giacomomellone/cicala/hardware/rev_b/pcb/models/README.md

# Component envelopes

These original, simplified STEP models restore the missing component
bodies in KiCad. The inherited models are generated by `../../../tools/pcb/make_component_models.py`
with CadQuery and use CERN-OHL-S-2.0, like the project hardware. They are
nominal envelopes with illustrative connector cavities; they are not supplier
models and do not establish assembled fit. No third-party CAD is redistributed.

| Model | Body envelope, mm | Dimensional reference |
| --- | --- | --- |
| HRO TYPE-C-31-M-12  | 8.94 × 7.35 × 3.26  | [HRO controlled drawing](https://datasheet.lcsc.com/datasheet/pdf/9e56b777c022540fcce7c7f67825f55e.pdf?productCode=C165948), including the 3.26 mm body height. |
| TPS63802 DLA0010A | 2 × 3 × 1 | [TI drawing 4223750/D](https://www.ti.com/lit/ds/symlink/tps63802.pdf), package outline; 1 mm maximum height. |
| Coilcraft XFL4015 | 4 × 4 × 1.6 | [Coilcraft drawing 769-2](https://www.coilcraft.com/getmedia/84927b8b-f089-421b-a7f4-a0fa23afe908/xfl4015.pdf); 4 ±0.3 mm body, 1.6 mm maximum height. |
| TDK VLS4012CX | 4 × 4 × 1.2 | [TDK part dimensions](https://product.tdk.com/en/search/inductor/inductor/smd/info?part_no=VLS4012CX-470M-1); 4 ±0.2 mm body, 1.2 mm maximum height. |
| Kingbright APBA2006 | 2 × 1.05 × 0.6 | [Kingbright DSAQ1665 revision 3A](https://www.kingbrightusa.com/images/catalog/SPEC/APBA2006SURKCGKC.pdf), page 1. Emission toward footprint +Y. |

Models use millimetres, footprint origin, model Y = negative footprint Y, and
positive Z above the mounting surface. Board-side transforms are applied by
KiCad. Open the project to resolve `${KIPRJMOD}/models/...` paths.

The PCB sits beside the protected pack. The case includes separate mated-JST
and wire-corridor reserves, and the USB opening admits a nominal 12 × 4 mm
overmold. The display's 180° flex loop reaches the top-side connector.
`hardware/tools/case/export_component_bounds.py` derives fitted component boxes from
the STEP export and fingerprints PCB placement and local model files. Capacitors use a 1.5 mm envelope, except the selected 1206 GRM31 parts at their 1.8 mm maximum.
Qualify actual mating parts, wire bends and print tolerances on prototypes.

## Rev B connector and switch envelopes

`Omron_B3F-4050.step` models the 12 × 12 mm switch body, 7.3 mm projected plunger and 3.5 mm terminal tails. It is an original nominal reference generated by `hardware/tools/rev_b/make_switch_model.py`, using the [Omron drawing](https://omronfs.omron.com/en_US/ecb/products/pdf/en-b3f.pdf). The purchased B32 caps are separate enclosure reference meshes; the PCB render shows the uncovered switches.

`Molex_503480-2400_envelope.step` reserves a 13.7 × 4 × 1.2 mm connector envelope from the [Molex drawing](https://www.molex.com/en-us/products/part-detail/5034802400). The standard KiCad JST SH model supplies J3. No supplier CAD is redistributed.
