giacomomellone/cicala/docs/sync_protocol.md

# Device sync protocol and bundle format

The website hosts one signed bundle per shipped language. A device downloads
only its installed languages, at most two.

## Manifest

Stable URL: `http://<site-domain>/device/manifest.json`

```json
{
  "schema": 4,
  "version": "2026.07.2",
  "min_fw": "0.2.0",
  "languages": {
    "en": {
      "url": "http://<site-domain>/device/bundle-en-2026.07.2.qdb",
      "size": 15166,
      "sha256": "9e2f…c41a",
      "sig": "base64-ed25519-signature-of-sha256",
      "count": 240
    }
  }
}
```

`count` is the number of stored questions. `sig` is an Ed25519 signature over the 32 raw bytes of the
bundle's SHA-256 digest. An unsigned development bundle uses `"sig": null`;
release firmware rejects it.

`url` points to the raw `.qdb`. `size`, `sha256`, and `sig` all describe those
bytes. A gzipped copy is also published for browsers and manual downloads.

Device endpoints use HTTP because the device has no trusted clock for TLS
certificate validation. Each bundle is protected by an Ed25519 signature and a
public key compiled into the firmware. The device rejects manifests whose
version is not newer than the installed version, which limits replay of an old
signed release.

## QDB4 bundle

**QDB4** is the flat binary form of the question database used by the device.
The format version is part of the magic bytes.

Two file extensions contain the same data:

| | What | Where |
| --- | --- | --- |
| `.qdb.gz` | gzip around the binary below | `dist/bundles/`, the website |
| `.qdb` | the binary itself | device downloads, storage, and firmware fixtures |

A `.qdb.gz` file is a deterministic gzip stream (`mtime=0`) around this flat
binary. Integers are little-endian and strings are UTF-8 without a terminator.

| Field |  Size | Meaning |
| --- | ----: | --- |
| magic | 4 | ASCII `QDB4` |
| version | 1 + n | u8 length, then release version |
| language | 1 + n | u8 length, then language code |
| count | 2 | u16 number of unique questions |
| then, per question | | |
| metadata | 1 | bits 0–1 are `depth - 1`; bit 2 is `sexual`; bit 3 is `dark`; bits 4–7 are zero |
| forms | 1 | form-tag bits in schema tag order minus the tone flags; bits 5–7 are zero |
| text | 2 + n | u16 byte length, then question text |

The bundle omits IDs because the physical device has no favorites, permalinks,
or human-visible question numbers. IDs remain in the repository and website.
Each record belongs to the single mixed stream. Dark and Sexual permissions
must be explicitly enabled for their respective flags, and Heavy must be enabled
for depth 3. Combinations require every permission. The forms byte carries
icebreaker, reflective, hypothetical, memory, and wouldyourather, in that order.

QDB3 is incompatible and rejected. Firmware 0.2.0 and question manifest schema 4
ship together. If a stored corpus is incompatible, the embedded QDB4 corpus is
used. RTC layout version 3 invalidates old category bags and filter state.

### Worked example

Language `en`, version `2026.07.2`, with one depth-2 question:

`When did you last sing out loud?`

Its metadata is `00000001`, and forms is `00000000`.

```text
51 44 42 34                                      "QDB4"
09 32 30 32 36 2E 30 37 2E 32                    len=9, "2026.07.2"
02 65 6E                                         len=2, "en"
01 00                                            count = 1
01                                               depth 2, no tone flags
00                                               no form tags
20 00                                            text length = 32
57 68 65 6E 20 64 69 64 20 79 6F 75 20 6C 61 73
74 20 73 69 6E 67 20 6F 75 74 20 6C 6F 75 64 3F
```

`tools/build_bundle.py` contains `parse_bundle()`, the executable reference
decoder. The tools unit suite round-trips both shipped languages.

### Two decoders

The writer and device reader implement the same format:

| | Where | Used by |
| --- | --- | --- |
| Writer + reference decoder | `tools/build_bundle.py` | the bundle build, the tools suite |
| Device reader | `core/src/qdb.cpp` | Zephyr and the CrossPoint fork |

The firmware suites read real bundles emitted by `build_bundle.py`.
`firmware/tests/qdb` also decodes the worked example above byte for byte.

The device reader checks every declared length at `open()` and rejects trailing
bytes. Its implementation is described in
[QDB reader](firmware_architecture.md#qdb-reader).

## Device flow

Holding Category and Next through boot opens the setup portal. Otherwise the
device joins a stored network after a cold boot, or after a button wakes it
during the external-power sync window. The portal status page can also request
a sync.

1. Fetch the manifest and check `schema`, `min_fw`, and that `version` is newer
   than the installed one.
2. Compare the release with each installed language.
3. Download a changed bundle and verify size, SHA-256, then signature.
4. Write a staging file and atomically rename it over the prior bundle.
5. Use the new bundle on the next requested draw. Automatic sync does not
   change the panel. A sync requested from the portal shows its result until the
   next press.

Any failure leaves the old bundle intact and retries during a later charging
window. A sync that fires by itself does not refresh the e-paper or take
attention from the current question.

## Keys

`tools/keygen.py` generates the Ed25519 pair through the system `openssl`.
The private key is a GitHub Actions secret. The public key is compiled into the
firmware. Key rotation requires a firmware release; devices without a valid new
bundle continue with their preloaded corpus.

The same key signs the OTA manifest, because it makes the same statement about
the same kind of artifact. It is _not_ the key that signs firmware images —
that one lives in the bootloader and is described in
[firmware_update.md](firmware_update.md).

## Firmware, which is the same shape

Firmware updates use `/device/firmware.json`, with the same fields and check
order. Corpus and firmware releases have separate manifests and version
comparisons. See
[firmware_update.md](firmware_update.md).
