giacomomellone/cicala/questions/de/STYLE.md

# Deutscher Stil-Leitfaden

So schreibst du eine Cicala-Frage auf Deutsch. Die Messlatte: Sie steht für sich, ist nicht mit Ja oder Nein zu erledigen und ist konkret
genug, um eine Geschichte anzustoßen. Die Begründung für diese Regeln steht in
der [Theorie](../../docs/theory.md).

## Stimme

- Sprich eine Person direkt an: **du**, immer klein geschrieben, niemals "Sie" oder "man".
- **Keine Anglizismen in Fragen.** Schreibe "Verabredung", nicht "Date". Die
  Die Metadaten-Schlüssel bleiben englisch.
- Eine gute deutsche Frage klingt, als hätte sie jemand am Küchentisch
  gestellt, unabhängig davon, ob sie auf Deutsch verfasst oder aus einer anderen
  Sprache übersetzt wurde.
- Maschinelle Übersetzungen sind Entwürfe. Sie müssen Sinn, Annahmen, Ton und
  mögliche Antworten des von einem Menschen verfassten Originals bewahren und
  das Original über `origin` verlinken. Klingt ein Entwurf nicht natürlich,
  überarbeite oder verwerfe ihn.
- Ein Fragezeichen, keine Ausrufezeichen, genau eine Frage pro Eintrag.

## Form

- Ziele auf 10–95 Zeichen; 140 ist die technische Obergrenze. Die Frage endet mit `?`.
- Beginne mit *Wann/Was/Wer/Wie/Welche* statt mit *Hast du/Bist du*; Letzteres lädt zu Ja/Nein ein.
- Konkret schlägt abstrakt: "Wann hast du zuletzt deine Meinung zu etwas Wichtigem geändert?" schlägt "Bist du aufgeschlossen?"
- Zweiteilige Fragen ("…, und was ist passiert?") sind gut, wenn der zweite Teil die Geschichte hervorlockt.
- Schreibe nur eine Frage, die auch die fragende Person beantworten könnte.
- Meide Superlative wie "beste", "schlimmste", "meiste" und "wenigste"; sie machen aus Erinnerung eine Rangliste.

## Eigenständige Fragen

Jede Frage wird einmal im gemischten Korpus gespeichert. Sie darf keine
bestimmte Beziehung oder gewählte Kategorie voraussetzen. Raum und sichtbare
Umgebung bleiben mögliche Ausgangspunkte.

## Tiefe

- `1`: wenig öffentliche Preisgabe.
- `2`: verlangt eine persönliche Einordnung.
- `3`: kann Verletzlichkeit, Konflikt, Angst, Verlust oder folgenreiche
  Preisgabe betreffen.

Tiefe und Ton sind getrennt. Die normale Wiedergabe nutzt 1 und 2. Schwer erlaubt Tiefe 3.
Düster und Sexuell sind davon unabhängige Freigaben.

## Schlagwörter

Sparsam verwenden, die meisten Fragen brauchen null oder eins. Die Schlüssel sind global englisch:

- `icebreaker`: sicher mit völlig Fremden in den ersten fünf Minuten.
- `reflective`: verlangt einen Blick nach innen; eine Denkpause ist zu erwarten.
- `sexual`: sexuelle Erfahrungen, Wünsche oder explizites Material. Erfordert
  Sexuell. Gewagtheit allein genügt nicht; alte `spicy`-Einträge brauchen
  eine ausdrückliche menschliche Neueinstufung.
- `dark`: düsteres, makabres oder verstörendes Material. Erfordert Düster.
- `hypothetical`: Gedankenspiele ("wenn…", "was würdest du…").
- `memory`: fragt nach einem konkreten erinnerten Moment.
- `wouldyourather`: eine erzwungene Wahl zwischen genau zwei Möglichkeiten.
