giacomomellone/cicala/questions/it/STYLE.md

# Guida di stile italiana

Come si scrive una domanda Cicala in italiano. Il criterio: funziona da sola, non si esaurisce con un sì o un no, ed è abbastanza concreta da
far partire un racconto. Il ragionamento dietro queste regole sta nella
[teoria](../../docs/theory.md).

## Voce

- Rivolgiti a una persona sola: **tu**, mai "Lei", mai "si" impersonale.
- **Niente anglicismi nelle domande.** Scrivi "appuntamento", non "date". Le
  chiavi dei metadati restano in inglese.
- Una buona domanda italiana suona come se qualcuno l'avesse posta a tavola,
  che sia stata scritta in italiano o tradotta da un'altra lingua.
- Le traduzioni automatiche sono bozze. Devono conservare senso, presupposti,
  tono e ventaglio di risposte plausibili dell'originale scritto da una
  persona, e collegare l'originale con `origin`. Se una bozza non suona
  naturale, riscrivila o scartala.
- Un punto interrogativo, nessun punto esclamativo, esattamente una domanda per
  voce.

## Forma

- Punta a 10–95 caratteri; 140 è il limite tecnico. La domanda finisce con `?`.
- Comincia con *Quando/Che cosa/Chi/Come/Quale* invece di *Hai/Sei*; questi
  ultimi invitano a un sì o un no.
- Concreto batte astratto: "Quando hai cambiato idea su qualcosa che contava?"
  batte "Sei una persona di mentalità aperta?"
- Le domande in due parti ("…, e com'è andata?") funzionano quando la seconda
  parte tira fuori il racconto.
- Scrivi solo domande a cui risponderesti anche tu.
- Evita i superlativi come "migliore", "peggiore", "di più" e "di meno":
  trasformano un ricordo in una classifica.

## Domande autonome

Ogni domanda si archivia una volta nel corpus misto. Non deve dipendere da una
relazione specifica o da una categoria scelta al tavolo. La stanza e ciò che si
vede intorno restano possibili punti di partenza.

## Profondità

- `1`: chiede poca esposizione pubblica.
- `2`: chiede una costruzione personale.
- `3`: può toccare vulnerabilità, conflitto, paura, perdita o rivelazioni che
  hanno conseguenze.

Profondità e tono sono indipendenti. La riproduzione normale usa 1 e 2. Pesante permette il 3.
Cupo e Sessuale sono permessi indipendenti.

## Etichette

Usale con parsimonia, la maggior parte delle domande ne vuole zero o una. Le
chiavi restano in inglese ovunque:

- `icebreaker`: sicura con estranei nei primi cinque minuti.
- `reflective`: chiede uno sguardo all'interno; è normale una pausa di
  riflessione.
- `sexual`: esperienze sessuali, desideri o materiale esplicito. Richiede
  Sessuale. Essere audace non basta; le vecchie voci `spicy` richiedono
  una riclassificazione umana esplicita.
- `dark`: materiale cupo, macabro o disturbante. Richiede Cupo.
- `hypothetical`: giochi mentali ("se…", "che cosa faresti…").
- `memory`: chiede un momento preciso che si ricorda.
- `wouldyourather`: una scelta forzata fra due sole possibilità.
