giacomomellone/cicala/hardware/rev_a/README.md

# Rev A

Original prototype: a 78 × 49 × 1.2 mm four-layer PCB in an
84 × 56 × 24.05 mm enclosure. Its electrical design is preserved.

- [PCB project and exports](pcb/README.md)
- [Enclosure and printable parts](case/README.md)
- [Bill of materials](BOM.md)
- [Manufacturing handoff](MANUFACTURING.md)
- [Verification and first power-up](REVIEW.md)

Run `just hw-review` from the repository root for the complete digital review.
Physical operation and printed fit still require prototype measurements.
