giacomomellone/cicala/hardware/rev_b/case/renders/wedge.png

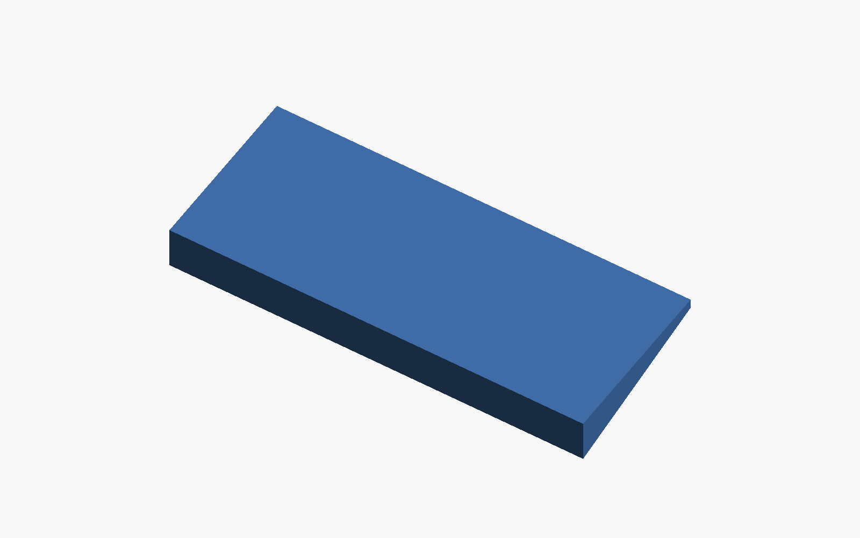
hardware/rev_b/case/renders/wedge.png
