giacomomellone/cicala/hardware/rev_b/pcb/renders/top.png

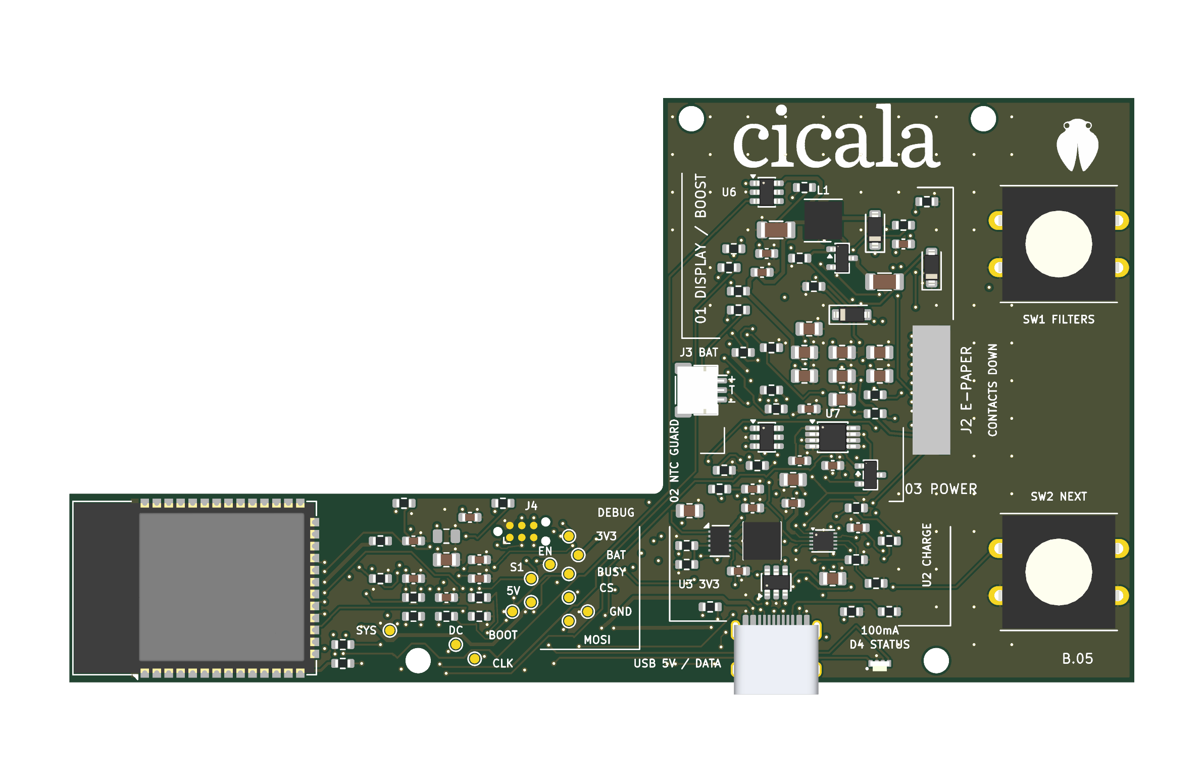
hardware/rev_b/pcb/renders/top.png
