giacomomellone/cicala/website/src/assets/device/pcb-bottom.webp

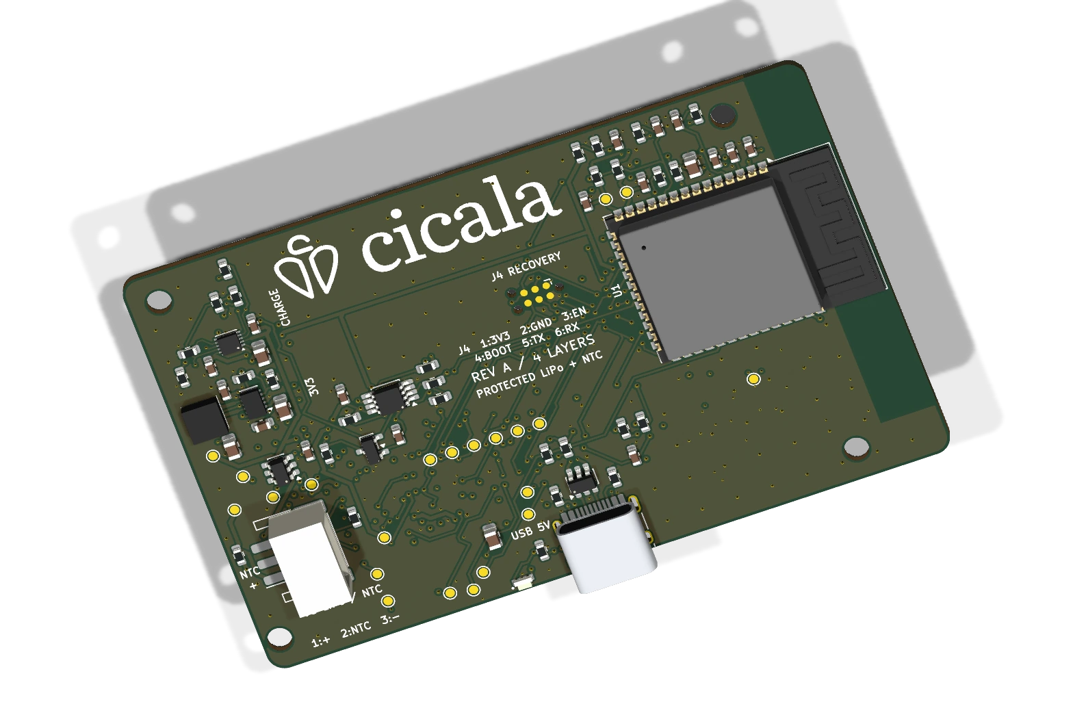
website/src/assets/device/pcb-bottom.webp
