giacomomellone/cicala/website/src/assets/device/pcb-top.webp

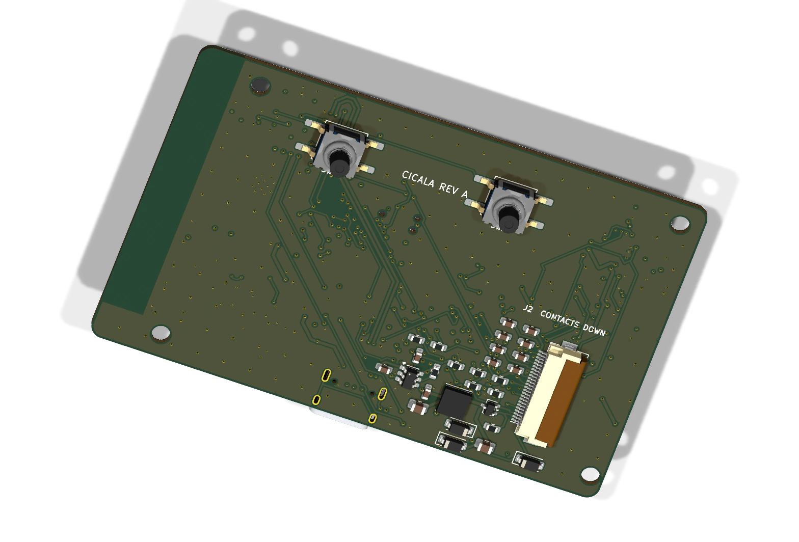
website/src/assets/device/pcb-top.webp
