giacomomellone/cicala/website/src/assets/device/x4pro-filters.png

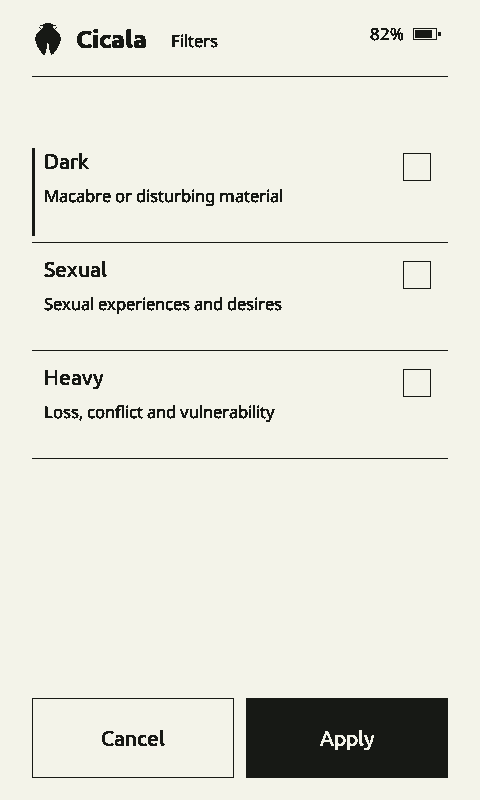
website/src/assets/device/x4pro-filters.png
