giacomomellone/cicala/website/src/assets/device/x4pro-home.png

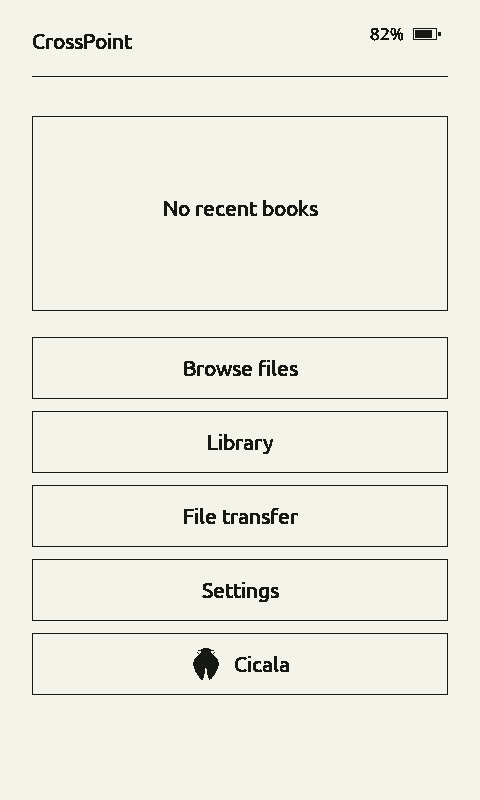
website/src/assets/device/x4pro-home.png
