giacomomellone/cicala/website/src/assets/device/x4pro-question.png

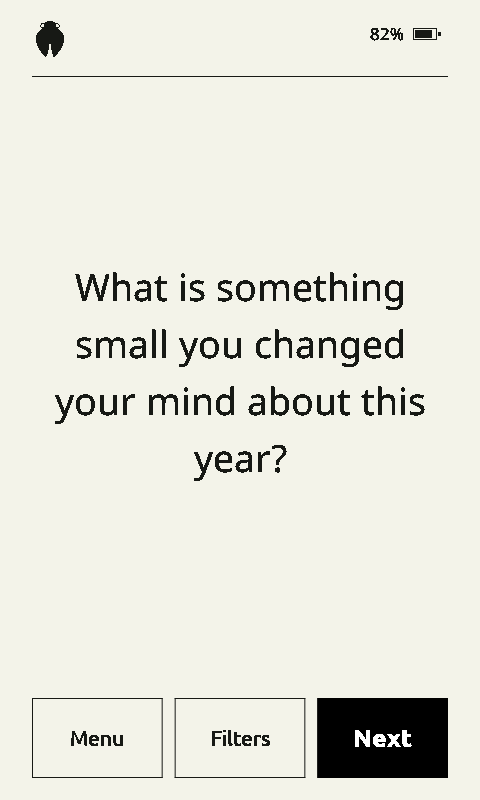
website/src/assets/device/x4pro-question.png
