giacomomellone/cicala/website/src/assets/landing/dopopranzo.webp

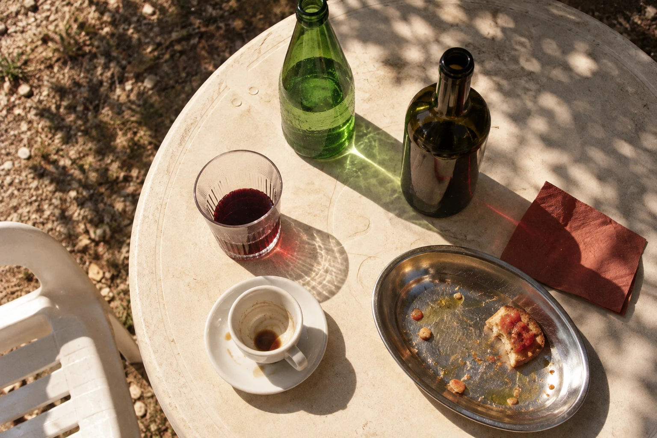
website/src/assets/landing/dopopranzo.webp
