giacomomellone/cicala/hardware/rev_b/case/exports/reference/cell_reference.3mf

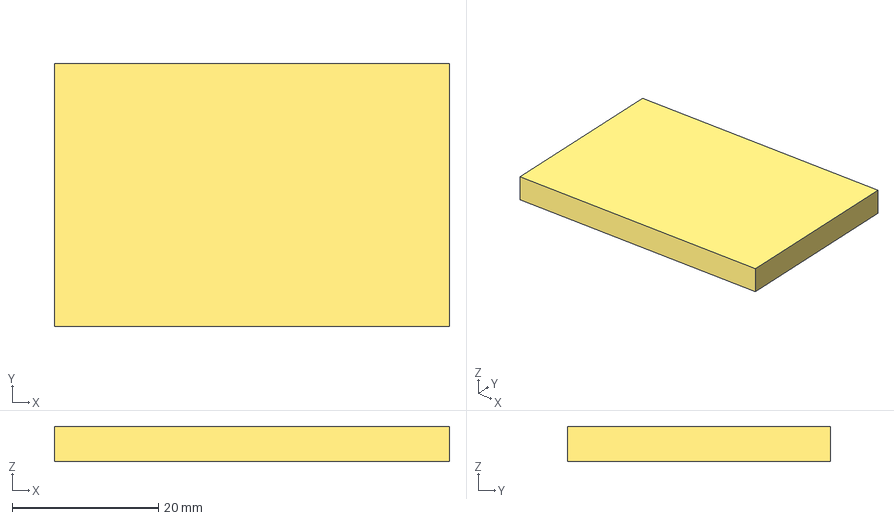
[picture p32: CAD file, 2026-09-16]
hardware/rev_b/case/exports/reference/cell_reference.3mf
54.0 x 36.0 x 4.80 mm
