giacomomellone/cicala/hardware/rev_b/case/exports/reference/pcb_reference.3mf

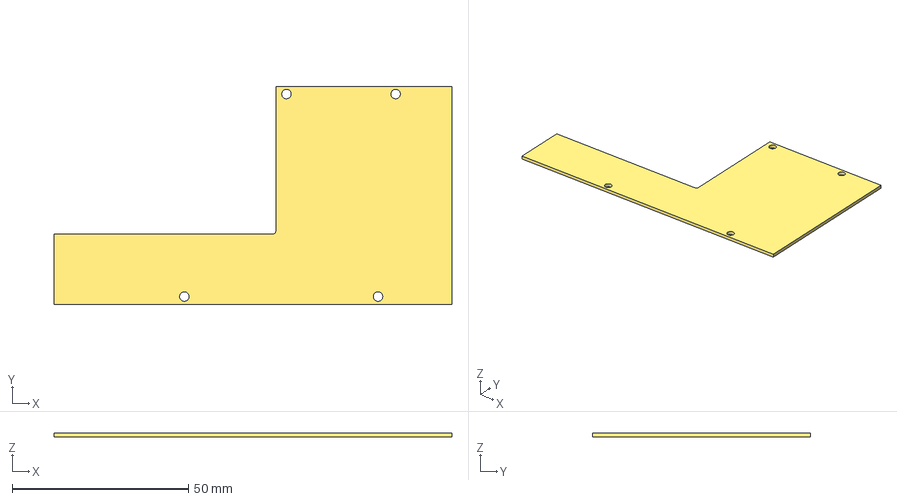
[picture p33: CAD file, 2026-09-16]
hardware/rev_b/case/exports/reference/pcb_reference.3mf
113.0 x 62.0 x 1.20 mm
