giacomomellone/cicala/hardware/rev_b/pcb/models/HRO_TYPE_C_31_M_12_envelope.step

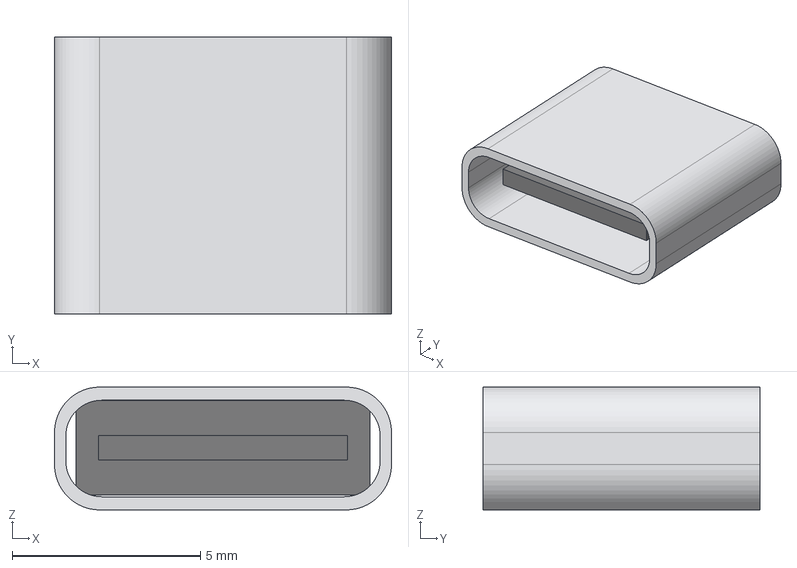
[picture p34: CAD file, 2026-09-07]
hardware/rev_b/pcb/models/HRO_TYPE_C_31_M_12_envelope.step
8.94 x 7.35 x 3.26 mm
