giacomomellone/cicala/hardware/rev_b/case/exports/reference/category_cap_reference.3mf

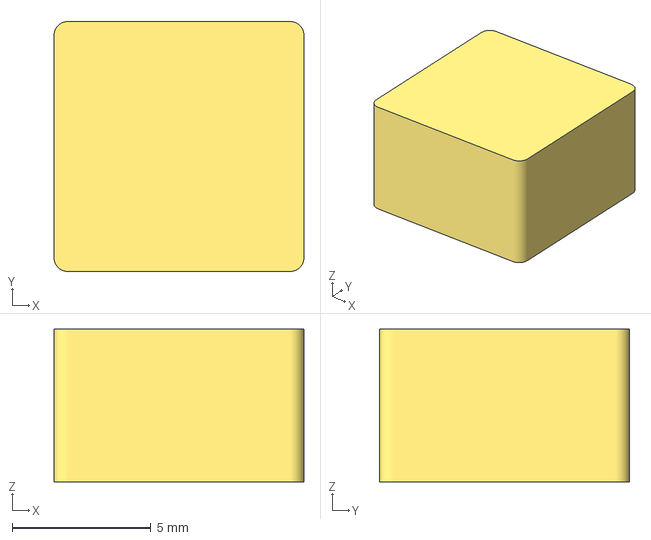
[picture p35: CAD file, 2026-09-16]
hardware/rev_b/case/exports/reference/category_cap_reference.3mf
9.00 x 9.00 x 5.50 mm
