giacomomellone/cicala/hardware/rev_b/pcb/models/Kingbright_APBA2006_envelope.step

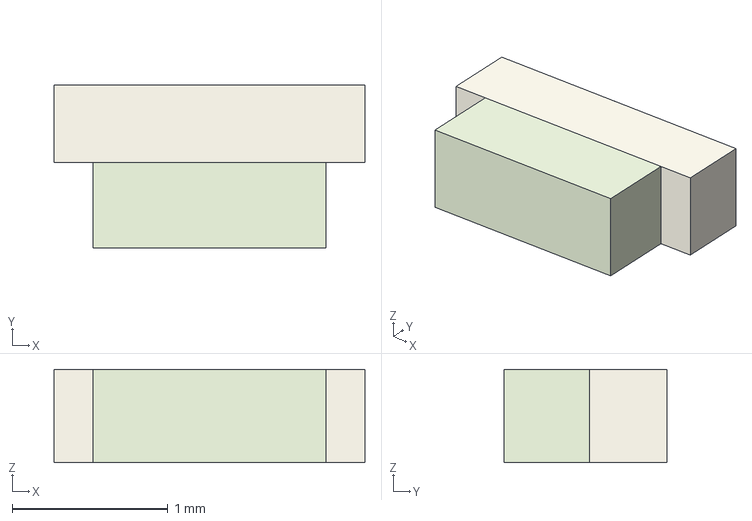
[picture p36: CAD file, 2026-09-07]
hardware/rev_b/pcb/models/Kingbright_APBA2006_envelope.step
2.00 x 1.05 x 0.6 mm
