giacomomellone/cicala/hardware/rev_b/case/exports/assembly/carrier_cover.3mf

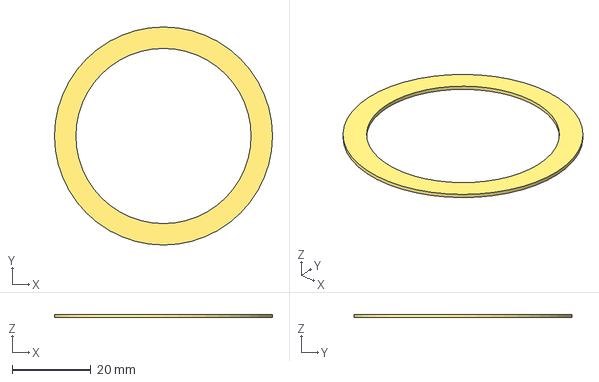
[picture p37: CAD file, 2026-09-16]
hardware/rev_b/case/exports/assembly/carrier_cover.3mf
55.5 x 55.5 x 0.85 mm
