giacomomellone/cicala/hardware/rev_b/case/exports/reference/next_cap_reference.3mf

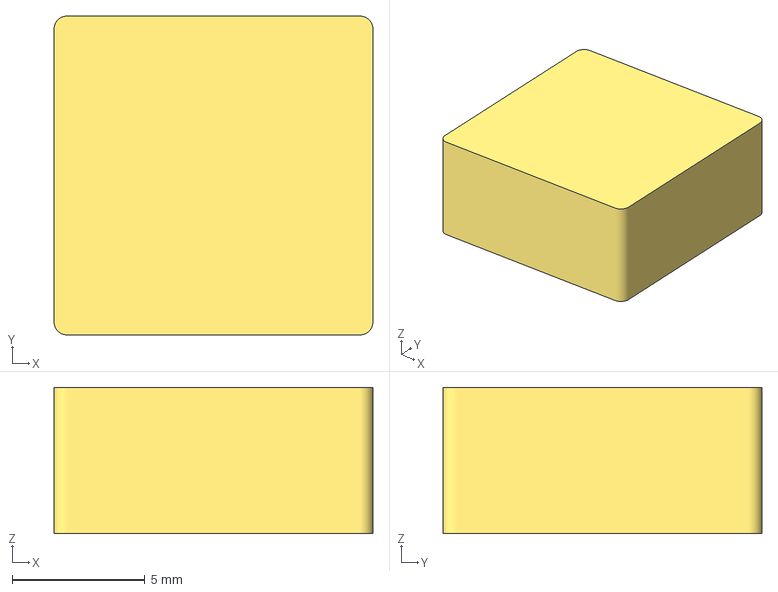
[picture p38: CAD file, 2026-09-16]
hardware/rev_b/case/exports/reference/next_cap_reference.3mf
12.0 x 12.0 x 5.50 mm
