giacomomellone/cicala/hardware/rev_b/pcb/models/Coilcraft_XFL4015_envelope.step

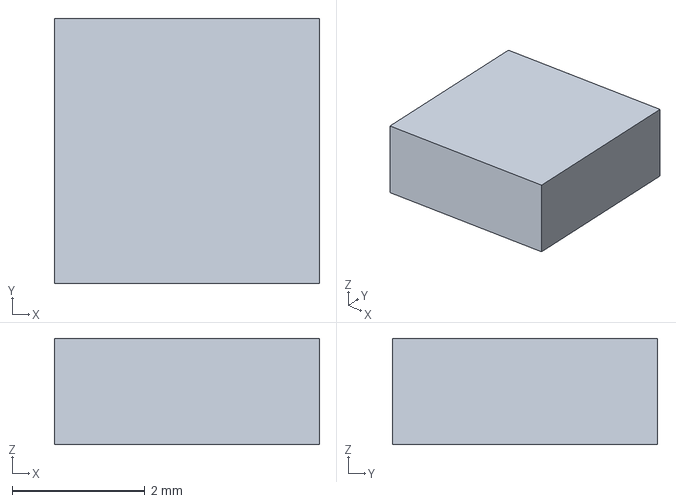
[picture p39: CAD file, 2026-09-07]
hardware/rev_b/pcb/models/Coilcraft_XFL4015_envelope.step
4.00 x 4.00 x 1.60 mm
