giacomomellone/cicala/hardware/rev_b/pcb/models/TDK_VLS4012CX_envelope.step

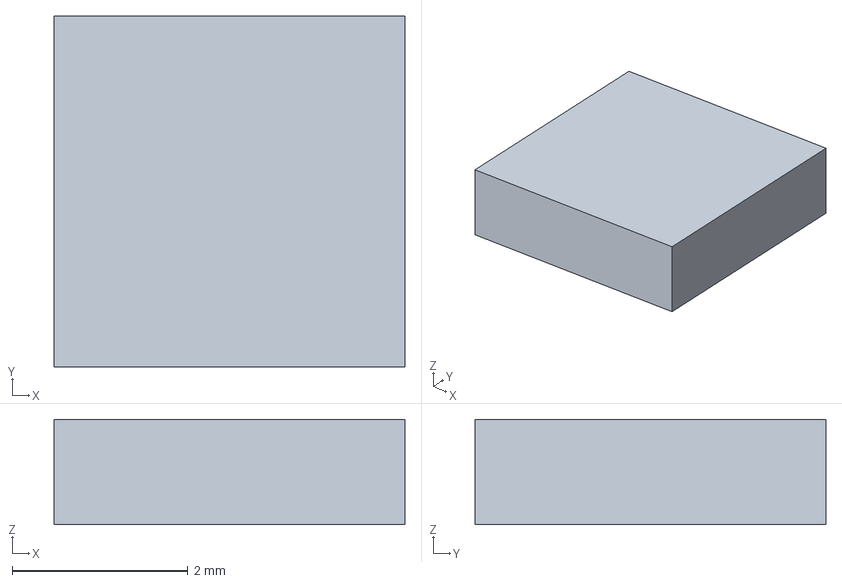
[picture p40: CAD file, 2026-09-07]
hardware/rev_b/pcb/models/TDK_VLS4012CX_envelope.step
4.00 x 4.00 x 1.20 mm
