giacomomellone/cicala/hardware/rev_b/case/pcb_component_bounds.scad

// Generated by export_component_bounds.py from the fitted KiCad STEP.
// placement_sha256: 7c28c48765177a294ebb8876503d3d054d704e8fcb34f9835404547f3ad9b8f7
// Capacitors reserve 1.5 mm, or 1.8 mm for GRM31CR71H475KA12L; switches have native
// enclosure references. Coordinates share the enclosure datum.
pcb_component_bounds = [
    ["C10", [83.0, 52.375, 5.815], [2.0, 1.25, 1.5]],
    ["C11", [74.7, 45.1, 5.815], [1.6, 0.8, 1.5]],
    ["C12", [76.2, 18.1, 5.815], [1.6, 0.8, 1.5]],
    ["C13", [75.7, 20.1, 5.815], [1.6, 0.8, 1.5]],
    ["C14", [90.7, 17.1, 5.815], [1.6, 0.8, 1.5]],
    ["C15", [76.4, 15.2, 5.815], [3.2, 1.6, 1.8]],
    ["C16", [87.9, 20.7, 5.815], [3.2, 1.6, 1.8]],
    ["C17", [84.0, 28.375, 5.815], [2.0, 1.25, 1.5]],
    ["C18", [84.0, 30.875, 5.815], [2.0, 1.25, 1.5]],
    ["C19", [80.0, 28.375, 5.815], [2.0, 1.25, 1.5]],
    ["C20", [88.0, 30.875, 5.815], [2.0, 1.25, 1.5]],
    ["C21", [88.0, 28.375, 5.815], [2.0, 1.25, 1.5]],
    ["C22", [80.5, 25.875, 5.815], [2.0, 1.25, 1.5]],
    ["C23", [80.0, 30.875, 5.815], [2.0, 1.25, 1.5]],
    ["C24", [84.0, 33.375, 5.815], [2.0, 1.25, 1.5]],
    ["C25", [45.7, 50.6, 5.815], [1.6, 0.8, 1.5]],
    ["C26", [42.2, 54.6, 5.815], [1.6, 0.8, 1.5]],
    ["C27", [38.7, 48.6, 5.815], [1.6, 0.8, 1.5]],
    ["C28", [38.7, 52.6, 5.815], [1.6, 0.8, 1.5]],
    ["C29", [44.7, 46.1, 5.815], [1.6, 0.8, 1.5]],
    ["C3", [45.7, 52.6, 5.815], [1.6, 0.8, 1.5]],
    ["C30", [42.0, 50.375, 5.815], [2.0, 1.25, 1.5]],
    ["C32", [83.2, 40.6, 5.815], [1.6, 0.8, 1.5]],
    ["C33", [79.7, 40.1, 5.815], [1.6, 0.8, 1.5]],
    ["C34", [80.7, 34.6, 5.815], [1.6, 0.8, 1.5]],
    ["C4", [85.9, 47.2, 5.815], [1.6, 0.8, 1.5]],
    ["C5", [78.8, 41.875, 5.815], [2.0, 1.25, 1.5]],
    ["C6", [79.0, 44.6, 5.815], [1.6, 0.8, 1.5]],
    ["C7", [74.7, 43.1, 5.815], [1.6, 0.8, 1.5]],
    ["C8", [67.8, 45.175, 5.815], [2.0, 1.25, 1.5]],
    ["C9", [73.2, 51.8, 5.815], [1.6, 0.8, 1.5]],
    ["D1", [84.1, 24.2, 5.815], [3.8, 1.6, 1.26]],
    ["D2", [93.7, 18.1, 5.815], [1.6, 3.8, 1.26]],
    ["D3", [87.7, 14.1, 5.815], [1.6, 3.8, 1.26]],
    ["D4", [88.0, 61.77, 5.815], [2.0, 1.05, 0.6]],
    ["J1", [73.53, 57.925, 5.815], [8.94, 7.35, 3.26]],
    ["J2", [92.48, 26.15, 5.815], [4.0, 13.7, 1.2]],
    ["J3", [67.525, 30.5, 5.815], [4.95, 5.0, 2.96]],
    ["L1", [81.0, 13.0, 5.815], [4.0, 4.0, 1.2]],
    ["L2", [74.5, 47.0, 5.815], [4.0, 4.0, 1.6]],
    ["Q1", [83.75, 17.5, 5.815], [2.5, 3.0, 1.2]],
    ["Q2", [86.75, 40.5, 5.815], [2.5, 3.0, 1.2]],
    ["R1", [85.2, 56.1, 5.815], [1.6, 0.8, 0.45]],
    ["R10", [75.2, 40.6, 5.815], [1.6, 0.8, 0.45]],
    ["R11", [71.2, 43.1, 5.815], [1.6, 0.8, 0.45]],
    ["R12", [85.7, 50.6, 5.815], [1.6, 0.8, 0.45]],
    ["R13", [85.7, 45.1, 5.815], [1.6, 0.8, 0.45]],
    ["R14", [67.7, 49.1, 5.815], [1.6, 0.8, 0.45]],
    ["R15", [67.7, 51.1, 5.815], [1.6, 0.8, 0.45]],
    ["R16", [89.2, 48.6, 5.815], [1.6, 0.8, 0.45]],
    ["R18", [73.2, 22.1, 5.815], [1.6, 0.8, 0.45]],
    ["R19", [79.7, 18.6, 5.815], [1.6, 0.8, 0.45]],
    ["R2", [89.2, 56.1, 5.815], [1.6, 0.8, 0.45]],
    ["R20", [81.2, 21.6, 5.815], [1.6, 0.8, 0.45]],
    ["R21", [38.7, 54.6, 5.815], [1.6, 0.8, 0.45]],
    ["R22", [48.2, 44.6, 5.815], [1.6, 0.8, 0.45]],
    ["R23", [45.7, 54.6, 5.815], [1.6, 0.8, 0.45]],
    ["R24", [42.2, 56.6, 5.815], [1.6, 0.8, 0.45]],
    ["R25", [37.7, 44.6, 5.815], [1.6, 0.8, 0.45]],
    ["R26", [38.7, 56.6, 5.815], [1.6, 0.8, 0.45]],
    ["R27", [72.7, 17.6, 5.815], [1.6, 0.8, 0.45]],
    ["R28", [80.2, 11.1, 5.815], [1.6, 0.8, 0.45]],
    ["R29", [90.7, 15.1, 5.815], [1.6, 0.8, 0.45]],
    ["R3", [31.2, 59.6, 5.815], [1.6, 0.8, 0.45]],
    ["R30", [73.2, 24.1, 5.815], [1.6, 0.8, 0.45]],
    ["R31", [72.2, 19.6, 5.815], [1.6, 0.8, 0.45]],
    ["R32", [76.7, 28.1, 5.815], [1.6, 0.8, 0.45]],
    ["R33", [45.7, 56.6, 5.815], [1.6, 0.8, 0.45]],
    ["R34", [73.7, 28.6, 5.815], [1.6, 0.8, 0.45]],
    ["R35", [77.2, 34.6, 5.815], [1.6, 0.8, 0.45]],
    ["R36", [87.7, 35.1, 5.815], [1.6, 0.8, 0.45]],
    ["R37", [93.2, 12.6, 5.815], [1.6, 0.8, 0.45]],
    ["R38", [87.7, 33.1, 5.815], [1.6, 0.8, 0.45]],
    ["R39", [76.7, 32.6, 5.815], [1.6, 0.8, 0.45]],
    ["R4", [31.2, 61.6, 5.815], [1.6, 0.8, 0.45]],
    ["R5", [35.2, 48.6, 5.815], [1.6, 0.8, 0.45]],
    ["R6", [35.2, 52.6, 5.815], [1.6, 0.8, 0.45]],
    ["R7", [71.7, 41.1, 5.815], [1.6, 0.8, 0.45]],
    ["R8", [87.8, 53.1, 5.815], [1.6, 0.8, 0.45]],
    ["R9", [70.2, 55.6, 5.815], [1.6, 0.8, 0.45]],
    ["U1", [3.5, 45.0, 5.815], [25.5, 18.0, 3.1]],
    ["U2", [81.9, 48.0125, 5.815], [2.2, 1.975, 0.8]],
    ["U3", [71.0, 47.5, 5.815], [2.0, 3.0, 1.0]],
    ["U4", [76.55, 52.0, 5.815], [2.9, 2.8, 1.55]],
    ["U5", [75.6, 36.55, 5.815], [2.8, 2.9, 1.55]],
    ["U6", [75.6, 10.55, 5.815], [2.8, 2.9, 1.55]],
    ["U7", [81.55, 36.5, 5.815], [4.9, 3.0, 1.35]]
];
