giacomomellone/cicala/firmware/app/include/input.h

/** The Category and Next buttons. */

#pragma once

#ifdef __cplusplus
extern "C" {
#endif

/** Check both buttons are present and start reporting. */
int cicala_input_init(void);

#ifdef __cplusplus
}
#endif
