giacomomellone/cicala/firmware/app/include/status.h

/** What the rest of the firmware tells the status LEDs. */

#pragma once

#include <stdbool.h>

#ifdef __cplusplus
extern "C" {
#endif

#ifdef CONFIG_CICALA_STATUS_LED

/** A sync or an update is moving bytes. */
void cicala_status_set_activity(bool busy);

/** The setup portal is on air, or has gone off it. */
void cicala_status_set_portal(bool on_air);

/** A press was turned away because the cell is under the refresh floor. */
void cicala_status_note_refresh_blocked(void);

/** Both pins low, and stop looking at them. */
void cicala_status_off(void);

#else

static inline void cicala_status_set_activity(bool busy)
{
    (void) busy;
}

static inline void cicala_status_set_portal(bool on_air)
{
    (void) on_air;
}

static inline void cicala_status_note_refresh_blocked(void) {}

static inline void cicala_status_off(void) {}

#endif /* CONFIG_CICALA_STATUS_LED */

#ifdef __cplusplus
}
#endif
