giacomomellone/cicala/firmware/app/include/sync.h

/** Bundle sync: fetch a manifest, and act on it if it says something new. */

#pragma once

#include <stdbool.h>
#include <stddef.h>
#include <stdint.h>

#ifdef __cplusplus
extern "C" {
#endif

/** How a sync ended, for the log and for the card. */
enum cicala_sync_result {
    /** Nothing to do: the manifest names the release already installed. */
    CICALA_SYNC_CURRENT = 0,
    /** A new corpus was verified and stored. */
    CICALA_SYNC_UPDATED,
    /** Something went wrong. */
    CICALA_SYNC_FAILED,
};

#ifdef CONFIG_CICALA_SYNC

/** Install a newer corpus and fill update metadata when provided. */
enum cicala_sync_result cicala_sync_run(const char *language, uint16_t *count, char *version,
                                        size_t version_size);

/** The release currently installed, or an empty string. */
const char *cicala_sync_installed_version(void);

#else

static inline enum cicala_sync_result cicala_sync_run(const char *language, uint16_t *count,
                                                      char *version, size_t version_size)
{
    (void) language;
    (void) count;
    (void) version;
    (void) version_size;

    return CICALA_SYNC_FAILED;
}

static inline const char *cicala_sync_installed_version(void)
{
    return "";
}

#endif /* CONFIG_CICALA_SYNC */

#ifdef __cplusplus
}
#endif
