giacomomellone/cicala/firmware/tests/integration/src/main.c

/* Exercise the real input-to-panel seams with emulated GPIO, ADC, and display. */

#include <zephyr/drivers/adc.h>
#include <zephyr/drivers/adc/adc_emul.h>
#include <zephyr/drivers/gpio.h>
#include <zephyr/drivers/gpio/gpio_emul.h>
#include <zephyr/init.h>
#include <zephyr/kernel.h>
#include <zephyr/sys/atomic.h>
#include <zephyr/ztest.h>

#include "channels.h"
#include "input.h"
#include "power.h"
#include "power_logic.h"
#include "status.h"

static const struct gpio_dt_spec category = GPIO_DT_SPEC_GET(DT_ALIAS(cicala_category), gpios);
static const struct gpio_dt_spec next_button = GPIO_DT_SPEC_GET(DT_ALIAS(cicala_next), gpios);

static const struct gpio_dt_spec led_red = GPIO_DT_SPEC_GET(DT_ALIAS(cicala_led_red), gpios);
static const struct gpio_dt_spec led_green = GPIO_DT_SPEC_GET(DT_ALIAS(cicala_led_green), gpios);

static const struct adc_dt_spec cell = ADC_DT_SPEC_GET(DT_PATH(zephyr_user));

static const struct gpio_dt_spec vbus = GPIO_DT_SPEC_GET(DT_PATH(zephyr_user), cicala_vbus_gpios);
static const struct gpio_dt_spec divider =
    GPIO_DT_SPEC_GET(DT_PATH(zephyr_user), cicala_battery_enable_gpios);

#define HAS_CHARGER DT_NODE_HAS_PROP(DT_PATH(zephyr_user), cicala_charger_status_gpios)
#if HAS_CHARGER
static const struct gpio_dt_spec stat1 =
    GPIO_DT_SPEC_GET_BY_IDX(DT_PATH(zephyr_user), cicala_charger_status_gpios, 0);
static const struct gpio_dt_spec stat2 =
    GPIO_DT_SPEC_GET_BY_IDX(DT_PATH(zephyr_user), cicala_charger_status_gpios, 1);

static void set_charger(bool high1, bool high2)
{
    zassert_ok(gpio_emul_input_set(stat1.port, stat1.pin, high1));
    zassert_ok(gpio_emul_input_set(stat2.port, stat2.pin, high2));
    k_msleep(CONFIG_CICALA_POWER_SAMPLE_MS * 3);
}
#endif

#define HEALTHY_MV 3900
/* Clear of the critical and plausible thresholds after ADC rounding. */
#define FLAT_MV 2800

/* The emulator supplies divider-tap voltage; power.c scales it to pack voltage. */
#define TAP_MV(pack) ((pack) * CONFIG_CICALA_POWER_DIVIDER_DEN / CONFIG_CICALA_POWER_DIVIDER_NUM)

static atomic_t tap_mv = ATOMIC_INIT(TAP_MV(HEALTHY_MV));
static atomic_t adc_reads;
static atomic_t adc_gate_errors;
static atomic_t adc_fail;

static int sample_gated_cell(const struct device *dev, unsigned int chan, void *data,
                             uint32_t *result)
{
    ARG_UNUSED(dev);
    ARG_UNUSED(chan);
    ARG_UNUSED(data);
    if (gpio_emul_output_get(divider.port, divider.pin) != 1) {
        atomic_inc(&adc_gate_errors);
    }
    atomic_inc(&adc_reads);
    *result = atomic_get(&tap_mv);
    return atomic_get(&adc_fail) ? -EIO : 0;
}

static int charge_the_cell(void)
{
    (void) adc_emul_value_func_set(cell.dev, cell.channel_id, sample_gated_cell, NULL);

    return 0;
}

/* Run before power.c samples the ADC at application priority. */
SYS_INIT(charge_the_cell, APPLICATION, 0);

static void set_cell_mv(uint16_t pack_mv)
{
    atomic_set(&tap_mv, TAP_MV(pack_mv));
    k_sleep(K_MSEC(CONFIG_CICALA_POWER_SAMPLE_MS * 3));
}

static void set_vbus(bool plugged)
{
    zassert_ok(gpio_emul_input_set(vbus.port, vbus.pin, plugged ? 1 : 0));
    k_sleep(K_MSEC(CONFIG_CICALA_POWER_SAMPLE_MS * 3));
}

static void settle_leds(void)
{
    /* Cases are unordered, so outlast any burst armed by a previous case. */
    k_sleep(K_MSEC(CONFIG_CICALA_STATUS_LED_BLINK_MS * 8));
}

/* Includes gpio-keys debounce and both application threads. */
#define PRESS_WAIT K_MSEC(CONFIG_CICALA_BUTTON_DEBOUNCE_MS + 300)

static struct cicala_question_msg last_question;

static struct cicala_question_msg first_question;
static bool have_first;

static int questions;
static int renders;
static int last_render_result;

static struct cicala_power_msg last_power;

static void observe(const struct zbus_channel *chan)
{
    if (chan == &chan_power) {
        last_power = *(const struct cicala_power_msg *) zbus_chan_const_msg(chan);
    } else if (chan == &chan_question) {
        last_question = *(const struct cicala_question_msg *) zbus_chan_const_msg(chan);
        questions++;

        if (!have_first) {
            first_question = last_question;
            have_first = true;
        }
    } else if (chan == &chan_render) {
        const struct cicala_render_msg *msg = zbus_chan_const_msg(chan);

        last_render_result = msg->result;
        renders++;
    }
}

ZBUS_LISTENER_DEFINE(test_obs, observe);
ZBUS_CHAN_ADD_OBS(chan_question, test_obs, 4);
ZBUS_CHAN_ADD_OBS(chan_render, test_obs, 4);
ZBUS_CHAN_ADD_OBS(chan_power, test_obs, 4);

static void press(const struct gpio_dt_spec *button)
{
    zassert_ok(gpio_emul_input_set(button->port, button->pin, 0));
    k_sleep(K_MSEC(80));
    zassert_ok(gpio_emul_input_set(button->port, button->pin, 1));
    k_sleep(PRESS_WAIT);
}

static void *suite_setup(void)
{
    /* Emulated active-low buttons start low. */
    zassert_ok(gpio_emul_input_set(category.port, category.pin, 1));
    zassert_ok(gpio_emul_input_set(next_button.port, next_button.pin, 1));

    zassert_ok(gpio_emul_input_set(vbus.port, vbus.pin, 0));
#if HAS_CHARGER
    set_charger(true, false);
#endif

    k_sleep(PRESS_WAIT);

    zassert_ok(cicala_input_init());
    k_sleep(PRESS_WAIT);

    return NULL;
}

static void suite_teardown(void *data)
{
    ARG_UNUSED(data);
    for (int i = 0; i < 200 && gpio_emul_output_get(divider.port, divider.pin) == 0; i++) {
        k_msleep(1);
    }
    cicala_power_prepare_sleep();
    cicala_status_off();
    atomic_val_t completed = atomic_get(&adc_reads);
    cicala_status_set_activity(true);
    cicala_status_set_portal(true);
    k_msleep(CONFIG_CICALA_POWER_SAMPLE_MS * 3);
    zassert_equal(atomic_get(&adc_reads), completed, "ADC rearmed after sleep preparation");
    zassert_equal(gpio_emul_output_get(divider.port, divider.pin), 0);
    zassert_equal(gpio_emul_output_get(led_red.port, led_red.pin), 0);
    zassert_equal(gpio_emul_output_get(led_green.port, led_green.pin), 0);
}

ZTEST_SUITE(cicala_integration, NULL, suite_setup, NULL, NULL, suite_teardown);

ZTEST(cicala_integration, test_adc_switch_closes_after_success_and_failure)
{
    set_cell_mv(HEALTHY_MV);
    for (int fail = 0; fail < 2; fail++) {
        atomic_set(&adc_fail, fail);
        atomic_val_t before = atomic_get(&adc_reads);
        for (int i = 0; i < 100 && atomic_get(&adc_reads) == before; i++) {
            k_msleep(10);
        }
        zassert_true(atomic_get(&adc_reads) > before, "ADC worker did not run");
        k_msleep(10);
        zassert_equal(gpio_emul_output_get(divider.port, divider.pin), 0,
                      "Divider must switch off even when conversion fails");
    }
    atomic_clear(&adc_fail);
    zassert_equal(atomic_get(&adc_gate_errors), 0, "ADC sampled an unpowered divider");
    set_cell_mv(HEALTHY_MV);
}

ZTEST(cicala_integration, test_boot_starts_the_mixed_stream)
{
    zassert_true(have_first);
    zassert_equal(first_question.kind, CICALA_CARD_QUESTION);
    zassert_equal(first_question.permissions, 0);
}

ZTEST(cicala_integration, test_filters_edit_a_draft_and_done_resumes_the_question)
{
    press(&next_button);
    struct cicala_question_msg before = last_question;
    press(&category);
    zassert_equal(last_question.kind, CICALA_CARD_FILTERS);
    zassert_equal(last_question.cursor, 0);
    press(&next_button);
    zassert_equal(last_question.permissions, before.permissions ^ 1);
    press(&next_button); // restore the draft
    for (int i = 1; i <= 3; i++) {
        press(&category);
        zassert_equal(last_question.cursor, i);
    }
    press(&next_button);
    zassert_equal(last_question.kind, CICALA_CARD_QUESTION);
    zassert_equal(last_question.len, before.len);
    zassert_mem_equal(last_question.text, before.text, before.len);
    zassert_equal(last_render_result, 0);
}

ZTEST(cicala_integration, test_next_draws_a_different_question)
{
    press(&next_button);
    zassert_equal(last_question.kind, CICALA_CARD_QUESTION);

    const uint32_t before_seq = last_question.seq;
    const uint16_t before_len = last_question.len;
    char before_text[CONFIG_CICALA_MAX_QUESTION_BYTES];

    memcpy(before_text, last_question.text, before_len);

    questions = 0;

    press(&next_button);

    zassert_equal(questions, 1, "one press is one question");
    zassert_true(last_question.seq > before_seq, "the sequence has to advance");

    const bool same =
        last_question.len == before_len && memcmp(last_question.text, before_text, before_len) == 0;

    zassert_false(same, "the bag must not hand back the question already on screen");
}

ZTEST(cicala_integration, test_a_flat_cell_leaves_the_question_on_the_panel)
{
    press(&next_button);

    const uint32_t drawn = last_question.seq;

    set_cell_mv(FLAT_MV);

    questions = 0;
    renders = 0;

    press(&next_button);

    zassert_equal(questions, 0, "nothing should have been published");
    zassert_equal(renders, 0, "and nothing should have reached the panel");
    zassert_equal(last_question.seq, drawn, "the glass still holds the last question");

    set_cell_mv(HEALTHY_MV);
}

ZTEST(cicala_integration, test_a_charged_cell_answers_again)
{
    set_cell_mv(FLAT_MV);

    questions = 0;
    press(&next_button);
    zassert_equal(questions, 0);

    set_cell_mv(HEALTHY_MV);

    press(&next_button);

    zassert_equal(questions, 1, "the press after a recovery is answered");
    zassert_equal(last_question.kind, CICALA_CARD_QUESTION);
    zassert_equal(last_render_result, 0);
}

ZTEST(cicala_integration, test_a_flat_cell_does_not_burn_a_question_from_the_bag)
{
    set_cell_mv(FLAT_MV);

    for (int i = 0; i < 5; i++) {
        press(&next_button);
    }

    set_cell_mv(HEALTHY_MV);

    questions = 0;
    press(&next_button);

    zassert_equal(questions, 1, "the bag still had something to give");
    zassert_equal(last_question.kind, CICALA_CARD_QUESTION);
}

ZTEST(cicala_integration, test_the_usb_bit_follows_the_pin)
{
    set_cell_mv(HEALTHY_MV);
    set_vbus(false);

    zassert_false(last_power.usb, "nothing is plugged in yet");

    set_vbus(true);

    zassert_true(last_power.usb, "plugging in has to reach the channel");
    zassert_equal(last_power.state, CICALA_POWER_CHARGING);

    set_vbus(false);

    zassert_false(last_power.usb, "and so does unplugging");
    zassert_equal(last_power.state, CICALA_POWER_NORMAL,
                  "unplugging re-derives from the cell rather than trusting where it was");
}

ZTEST(cicala_integration, test_external_power_answers_a_press_the_cell_would_not)
{
    set_cell_mv(FLAT_MV);

    questions = 0;
    press(&next_button);
    zassert_equal(questions, 0, "on the cell alone this press is refused");

    set_vbus(true);

    questions = 0;
    press(&next_button);

    zassert_equal(questions, 1, "external power pays for the refresh");
    zassert_equal(last_question.kind, CICALA_CARD_QUESTION);
    zassert_equal(last_render_result, 0);

    set_cell_mv(HEALTHY_MV);
    set_vbus(false);
}

ZTEST(cicala_integration, test_charge_indicator_follows_available_evidence)
{
    set_cell_mv(HEALTHY_MV);
    set_vbus(true);
    settle_leds();

    zassert_true(gpio_emul_output_get(led_red.port, led_red.pin) > 0, "charging is steady red");
    zassert_equal(gpio_emul_output_get(led_green.port, led_green.pin), 0);

    set_cell_mv(CONFIG_CICALA_POWER_FULL_MV + 50);

#if HAS_CHARGER
    zassert_equal(last_power.state, CICALA_POWER_CHARGING,
                  "high voltage must not override charging-in-progress status");
    zassert_true(gpio_emul_output_get(led_red.port, led_red.pin) > 0);
    zassert_equal(gpio_emul_output_get(led_green.port, led_green.pin), 0);
#else
    zassert_true(gpio_emul_output_get(led_green.port, led_green.pin) > 0, "and full is green");
    zassert_equal(gpio_emul_output_get(led_red.port, led_red.pin), 0);
#endif

    set_vbus(false);
    set_cell_mv(HEALTHY_MV);

    zassert_equal(gpio_emul_output_get(led_red.port, led_red.pin), 0,
                  "unplugged and healthy shows nothing at all");
    zassert_equal(gpio_emul_output_get(led_green.port, led_green.pin), 0);
}

#if HAS_CHARGER
ZTEST(cicala_integration, test_charger_status_pins_reach_state_and_leds)
{
    set_cell_mv(HEALTHY_MV);
    set_vbus(true);
    settle_leds();
    set_charger(true, true);
    zassert_equal(last_power.state, CICALA_POWER_EXTERNAL_IDLE);
    zassert_equal(last_power.charger, CICALA_CHARGER_IDLE);

    set_charger(false, true);
    zassert_equal(last_power.state, CICALA_POWER_CHARGE_FAULT);
    zassert_equal(last_power.charger, CICALA_CHARGER_RECOVERABLE_FAULT);
    zassert_true(cicala_power_external());
    zassert_true(cicala_power_refresh_allowed());

    set_charger(false, false);
    zassert_equal(last_power.state, CICALA_POWER_CHARGE_FAULT);
    zassert_equal(last_power.charger, CICALA_CHARGER_LATCHED_FAULT,
                  "fault detail must publish even at unchanged cell voltage");
    bool lit = false;
    bool dark = false;
    for (int i = 0; i < 200 && !(lit && dark); i++) {
        int red = gpio_emul_output_get(led_red.port, led_red.pin);
        lit |= red > 0;
        dark |= red == 0;
        zassert_equal(gpio_emul_output_get(led_green.port, led_green.pin), 0);
        k_msleep(10);
    }
    zassert_true(lit && dark, "charger faults pulse red");

    set_charger(true, false);
    zassert_equal(last_power.state, CICALA_POWER_CHARGING);
    zassert_true(gpio_emul_output_get(led_red.port, led_red.pin) > 0);
    set_vbus(false);
}
#endif

ZTEST(cicala_integration, test_the_portal_shows_amber)
{
    set_cell_mv(HEALTHY_MV);
    settle_leds();

    cicala_status_set_portal(true);
    k_sleep(K_MSEC(CONFIG_CICALA_STATUS_LED_BLINK_MS));

    zassert_true(gpio_emul_output_get(led_red.port, led_red.pin) > 0, "amber is both lit");
    zassert_true(gpio_emul_output_get(led_green.port, led_green.pin) > 0, "amber is both lit");

    cicala_status_set_portal(false);
    k_sleep(K_MSEC(CONFIG_CICALA_STATUS_LED_BLINK_MS));

    zassert_equal(gpio_emul_output_get(led_red.port, led_red.pin), 0,
                  "and it goes away when the portal does");
    zassert_equal(gpio_emul_output_get(led_green.port, led_green.pin), 0);
}

ZTEST(cicala_integration, test_a_refused_press_is_answered_on_the_red_led)
{
    set_cell_mv(HEALTHY_MV);
    settle_leds();

    zassert_equal(gpio_emul_output_get(led_red.port, led_red.pin), 0,
                  "a healthy cell shows nothing at all");
    zassert_equal(gpio_emul_output_get(led_green.port, led_green.pin), 0);

    set_cell_mv(FLAT_MV);

    press(&next_button);

    bool seen_lit = false;
    bool seen_dark = false;

    /* press() has already consumed part of the blink burst. */
    for (int i = 0; i < 60 && !(seen_lit && seen_dark); i++) {
        if (gpio_emul_output_get(led_red.port, led_red.pin) > 0) {
            seen_lit = true;
        } else {
            seen_dark = true;
        }

        k_sleep(K_MSEC(CONFIG_CICALA_STATUS_LED_BLINK_MS / 4));
    }

    zassert_true(seen_lit, "a refused press should say so");
    zassert_true(seen_dark, "and it should blink rather than latch on");

    zassert_equal(gpio_emul_output_get(led_green.port, led_green.pin), 0,
                  "green means charged, and this cell is the opposite");

    set_cell_mv(HEALTHY_MV);
    k_sleep(K_MSEC(CONFIG_CICALA_STATUS_LED_BLINK_MS * 8));

    zassert_equal(gpio_emul_output_get(led_red.port, led_red.pin), 0,
                  "and the burst ends rather than running forever");
}
