giacomomellone/cicala/firmware/tests/input/src/main.c

#include <zephyr/drivers/gpio.h>
#include <zephyr/drivers/gpio/gpio_emul.h>
#include <zephyr/kernel.h>
#include <zephyr/ztest.h>

#include "channels.h"
#include "input.h"

static const struct gpio_dt_spec category = GPIO_DT_SPEC_GET(DT_ALIAS(cicala_category), gpios);
static const struct gpio_dt_spec next_button = GPIO_DT_SPEC_GET(DT_ALIAS(cicala_next), gpios);

#define PRESS_WAIT K_MSEC(CONFIG_CICALA_BUTTON_DEBOUNCE_MS + 150)

static int category_publishes;
static int next_publishes;
static struct cicala_filters_msg last_category;
static struct cicala_next_msg last_next;

static void observe(const struct zbus_channel *chan)
{
    if (chan == &chan_filters) {
        category_publishes++;
        last_category = *(const struct cicala_filters_msg *) zbus_chan_const_msg(chan);
    } else if (chan == &chan_next) {
        next_publishes++;
        last_next = *(const struct cicala_next_msg *) zbus_chan_const_msg(chan);
    }
}

ZBUS_LISTENER_DEFINE(test_obs, observe);
ZBUS_CHAN_ADD_OBS(chan_filters, test_obs, 4);
ZBUS_CHAN_ADD_OBS(chan_next, test_obs, 4);

static void press(const struct gpio_dt_spec *button, bool down)
{
    zassert_ok(gpio_emul_input_set(button->port, button->pin, down ? 0 : 1));
}

static void tap(const struct gpio_dt_spec *button, int hold_ms)
{
    press(button, true);
    k_sleep(K_MSEC(hold_ms));
    press(button, false);
    k_sleep(PRESS_WAIT);
}

static void *suite_setup(void)
{
    press(&category, false);
    press(&next_button, false);
    k_sleep(PRESS_WAIT);

    zassert_ok(cicala_input_init());

    return NULL;
}

static void before_each(void *fixture)
{
    ARG_UNUSED(fixture);

    category_publishes = 0;
    next_publishes = 0;
}

ZTEST_SUITE(cicala_input, NULL, suite_setup, before_each, NULL, NULL);

ZTEST(cicala_input, test_one_category_press_is_one_event)
{
    tap(&category, 60);

    zassert_equal(category_publishes, 1, "one press is one event");
    zassert_equal(next_publishes, 0, "and it must not look like Next");
}

ZTEST(cicala_input, test_one_next_press_is_one_event)
{
    tap(&next_button, 60);

    zassert_equal(next_publishes, 1, "one press is one event");
    zassert_equal(category_publishes, 0, "and it must not look like Category");
}

ZTEST(cicala_input, test_a_press_is_reported_on_release)
{
    press(&next_button, true);
    k_sleep(PRESS_WAIT);

    zassert_equal(next_publishes, 0, "held down is not yet a press");

    press(&next_button, false);
    k_sleep(PRESS_WAIT);

    zassert_equal(next_publishes, 1);
    zassert_true(last_next.duration_ms >= (uint32_t) CONFIG_CICALA_BUTTON_DEBOUNCE_MS,
                 "the reported duration should cover the hold, got %u ms", last_next.duration_ms);
}

ZTEST(cicala_input, test_a_long_press_is_still_one_event)
{
    tap(&next_button, 900);

    zassert_equal(next_publishes, 1, "long press is Next, same as a short one");
}

ZTEST(cicala_input, test_the_buttons_are_independent)
{
    press(&category, true);
    k_sleep(PRESS_WAIT);

    tap(&next_button, 60);

    press(&category, false);
    k_sleep(PRESS_WAIT);

    zassert_equal(next_publishes, 1, "Next reports while Category is held");
    zassert_equal(category_publishes, 1, "and Category reports when it is let go");
    zassert_true(last_category.duration_ms > 0);
}
