giacomomellone/cicala/firmware/tests/smoke/src/main.cpp

#include <zephyr/ztest.h>

ZTEST_SUITE(cicala_smoke, NULL, NULL, NULL, NULL, NULL);

ZTEST(cicala_smoke, test_harness_runs)
{
    zassert_true(true, "ztest runs on native_sim");
}

ZTEST(cicala_smoke, test_cpp17_available)
{
    constexpr struct {
        int deck;
        int depth;
    } q{5, 2};
    const auto [deck, depth] = q;

    zassert_equal(deck, 5);
    zassert_equal(depth, 2);
}
