giacomomellone/cicala/firmware/tests/soak/src/main.c

#include <zephyr/drivers/gpio.h>
#include <zephyr/drivers/gpio/gpio_emul.h>
#include <zephyr/kernel.h>
#include <zephyr/ztest.h>

#include "channels.h"
#include "input.h"

static const struct gpio_dt_spec next_button = GPIO_DT_SPEC_GET(DT_ALIAS(cicala_next), gpios);

#define RUN_WAIT K_MSEC(10 * CONFIG_CICALA_DEBUG_SOAK_INTERVAL_MS + 1000)

#define EXPECTED_RENDERS 6

static uint32_t questions;
static uint32_t renders;
static uint32_t full_renders;
static uint32_t failed_renders;
static uint32_t last_seq;
static bool seq_repeated;

static void observe(const struct zbus_channel *chan)
{
    if (chan == &chan_question) {
        const struct cicala_question_msg *msg = zbus_chan_const_msg(chan);

        if (msg->seq <= last_seq) {
            seq_repeated = true;
        }

        last_seq = msg->seq;
        questions++;
    } else if (chan == &chan_render) {
        const struct cicala_render_msg *msg = zbus_chan_const_msg(chan);

        renders++;

        if (msg->was_full) {
            full_renders++;
        }

        if (msg->result != 0) {
            failed_renders++;
        }
    }
}

ZBUS_LISTENER_DEFINE(test_obs, observe);
ZBUS_CHAN_ADD_OBS(chan_question, test_obs, 4);
ZBUS_CHAN_ADD_OBS(chan_render, test_obs, 4);

static void *suite_setup(void)
{
    zassert_ok(gpio_emul_input_set(next_button.port, next_button.pin, 1));
    k_sleep(K_MSEC(100));

    zassert_ok(cicala_input_init());

    return NULL;
}

ZTEST_SUITE(cicala_soak, NULL, suite_setup, NULL, NULL, NULL);

ZTEST(cicala_soak, test_the_chain_runs_hands_off)
{
    k_sleep(RUN_WAIT);

    zassert_true(renders >= EXPECTED_RENDERS,
                 "the chain stopped after %u refreshes; the soak run needs it to keep pressing",
                 renders);
    zassert_true(questions >= renders, "a render arrived for a question nobody published");
    zassert_false(seq_repeated, "each press must draw a new card, not redraw the last one");
    zassert_equal(failed_renders, 0, "no refresh should have failed");

    zassert_equal(full_renders, 1,
                  "soak.conf should have suppressed every full refresh but the "
                  "first, and %u came through",
                  full_renders);
}
